Fabian1234567/Handroboter/Kostentabelle_FabianExel.pdf

Tabelle1

Kostentabelle SIA Fabian Exel
Projekt: Roboterarm Handschuh
Teil | Menge | Preis einzelnd | Preis zusammen
Servo | 3 | 15,00 € | 45,00 €
Holzplatte | 1 | 2,00 € | 2,00 €
Ständer | 1 | 1,00 € | 1,00 €
Arduino Mega | 1 | 60,00 € | 60,00 €
Handschuh | 1 | 5,00 € | 5,00 €
Kabel | | 3,00 € | 3,00 €
diverses anderes Holz | | 5,00 € | 5,00 €
Metallplatten | | 7,00 € | 7,00 €
Metallstangen | | 3,00 € | 3,00 €
Potentiometer | 2 | 0,50 € | 1,00 €
Neigunngssensor | 1 | 0,50 € | 0,50 €
diverse Schrauben | | 1,00 € | 1,00 €
Zahnräder | 3 | 0,20 € | 0,60 €
Summe: | 134,10 €

* Alle Angaben sind Schätzwerte, da die Sachen überwiegend schon vorhanden sind
