Fabian1234567/Handroboter/Abschlusspräsentation.pdf

# Was wäre, wenn Sie hier sitzen bleiben könnten, während Sie in einem anderen Klassenzimmer auf die Tafel schreiben?

# Die Lösung:

Der Robotergreifer,

# der sich wie eine Hand bewegt

# Ein SIA Projekt von Fabian Exel am Gustav Stresemann Gymnasium Fellbach-Schmiden

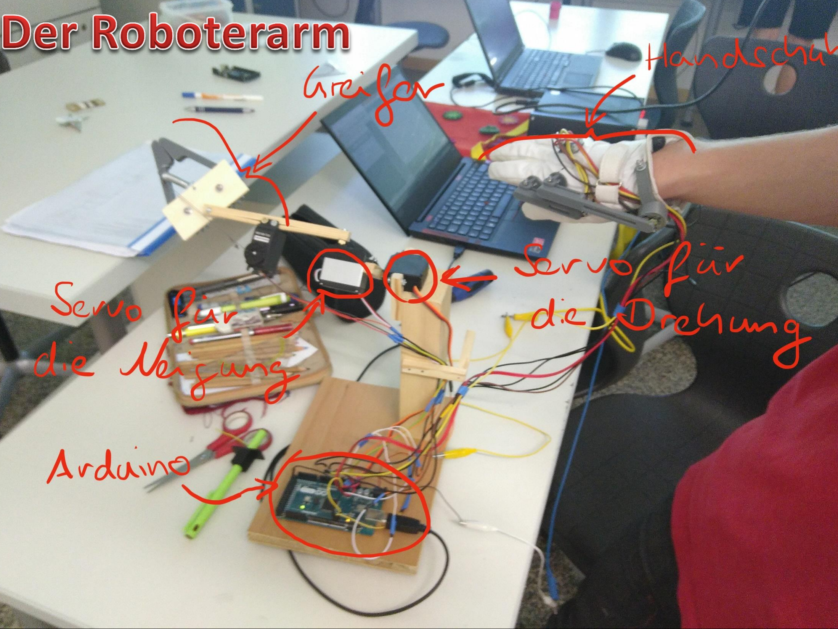
[picture p3: page 3]

# Handschuh

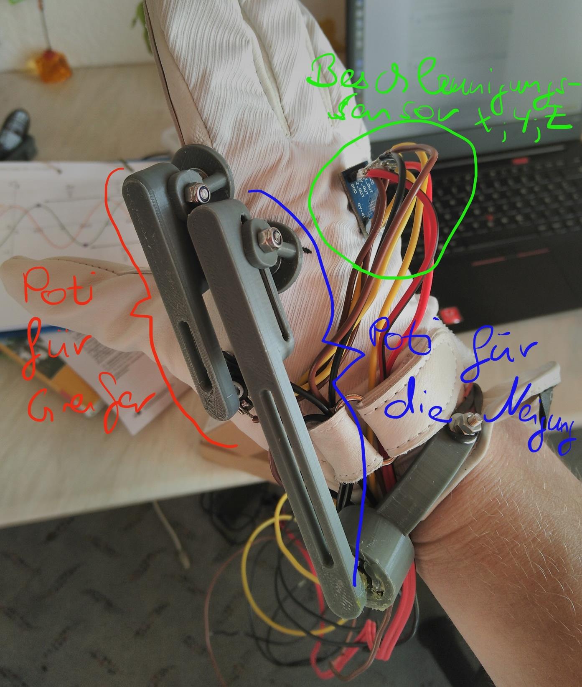
[picture p4: page 4]

# Schaltplan

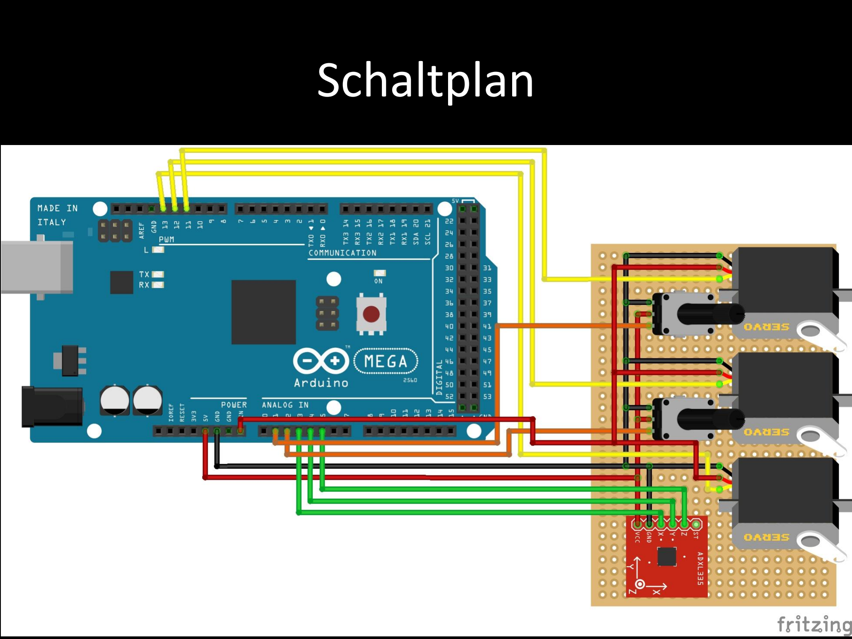
[picture p5: page 5]

# EDV

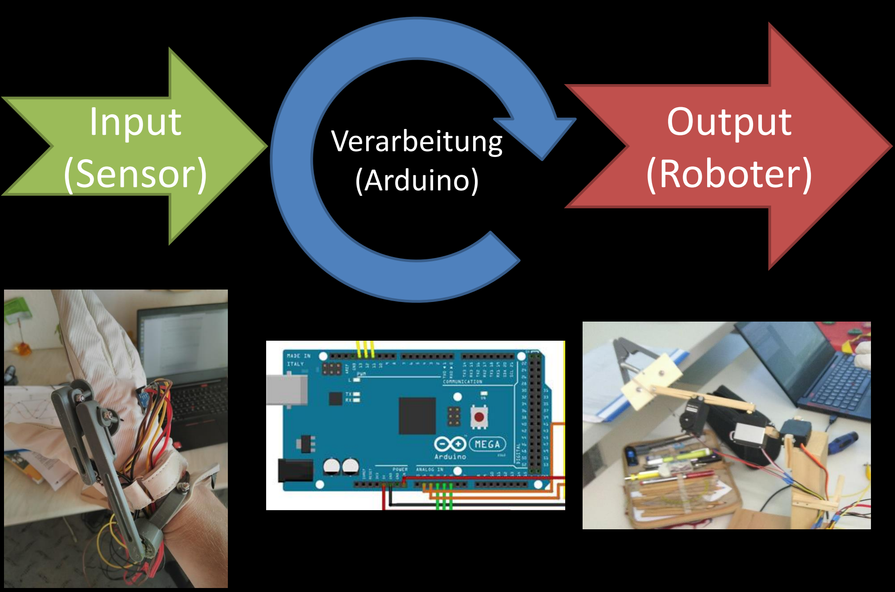
[picture p6: figure]
Input (Sensor); Verarbeitung (Arduino); Output (Roboter)

# Greifer

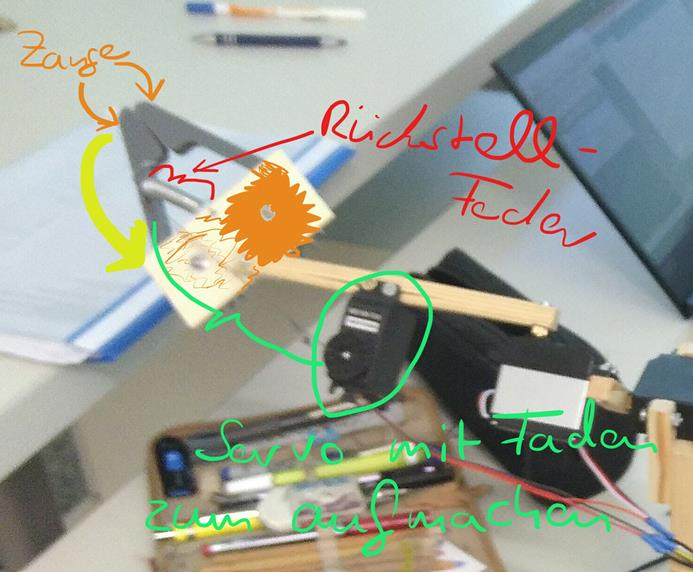
[picture p7: page 7]

# Warum Servo?

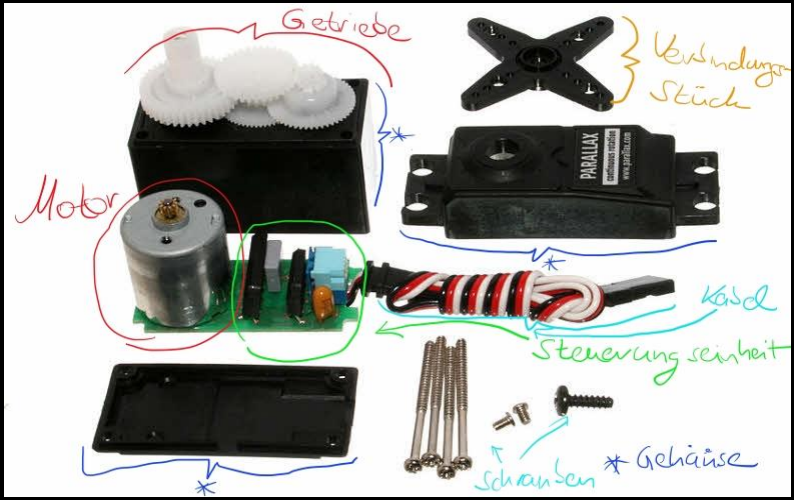
[picture p8: figure]

(https://www.precifast.de/servomotor-funktion-ansteuern-anschliessen/)

# Regelkreis des Servos

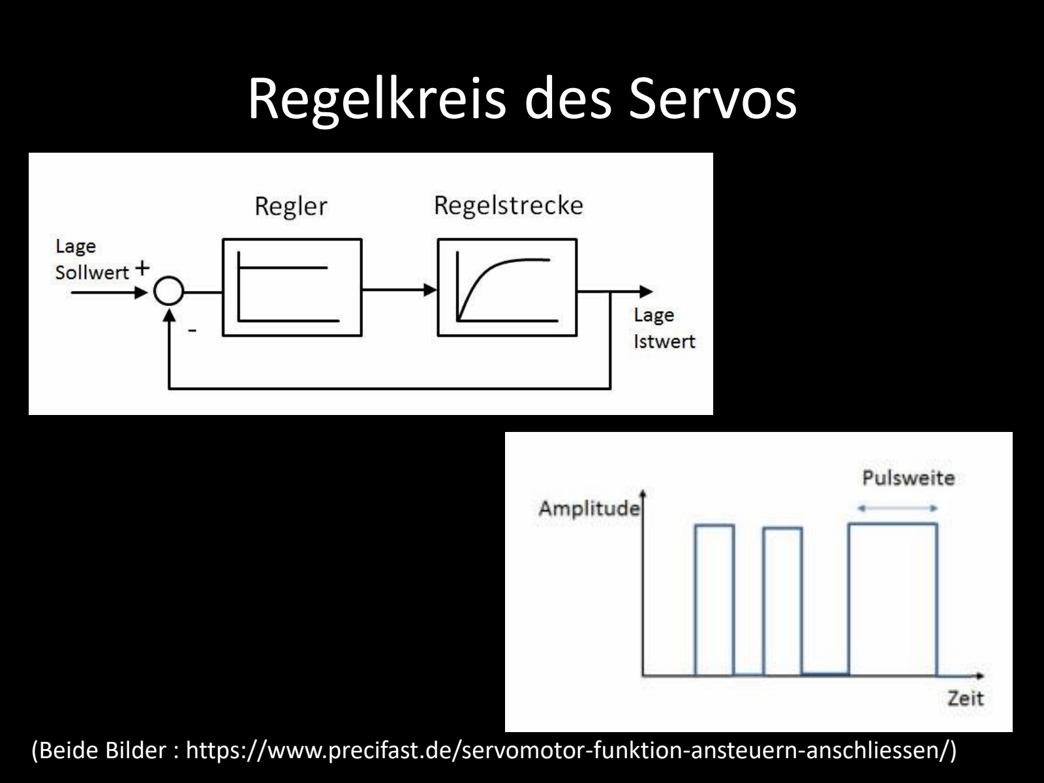
[picture p9: page 9]

(Beide Bilder : https://www.precifast.de/servomotor-funktion-ansteuern-anschliessen/)

# Warum Beschleunigungssensor?

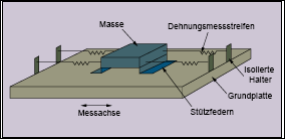
[picture p10: figure]

(https://www.omega.de/prodinfo/beschleunigungsmesser-vibrationsaufnehmer.html)

# Programmcode

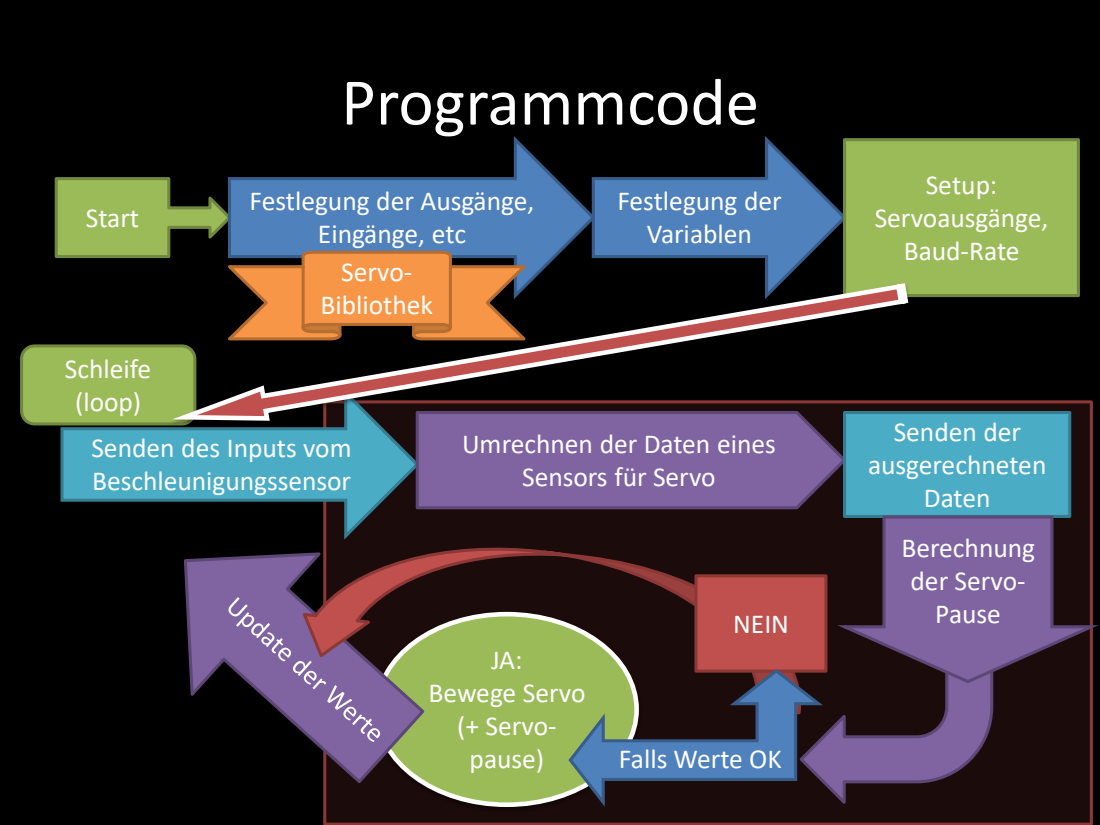
[picture p11: page 11]
Start; Festlegung der Ausgänge,; Eingänge, etc; Festlegung der Variablen; Servo- Bibliothek; Setup: Servoausgänge, Baud-Rate; Senden der ausgerechneten Daten; JA: Bewege Servo (+ Servo- pause); NEIN; Berechnung der Servo- Pause

Schleife
(loop)
Senden des Inputs vom
Beschleunigungssensor

Umrechnen der Daten eines
Sensors für Servo

Falls Werte OK

# Der wichtigste Baustein des Programms

- neigung = map(analogRead(accYPin), 270, 410, 30, 330);
- Serial.print(" Servo Neigung: ");
- Serial.print(neigung);

## - pause_neigung = abs(neigung - neigung_alt)

* 5;

## - if (pause_neigung <= 80 && neigung > 0){

- third.write(neigung);
- delay(pause_neigung);
- }
- neigung_alt = neigung;
- }

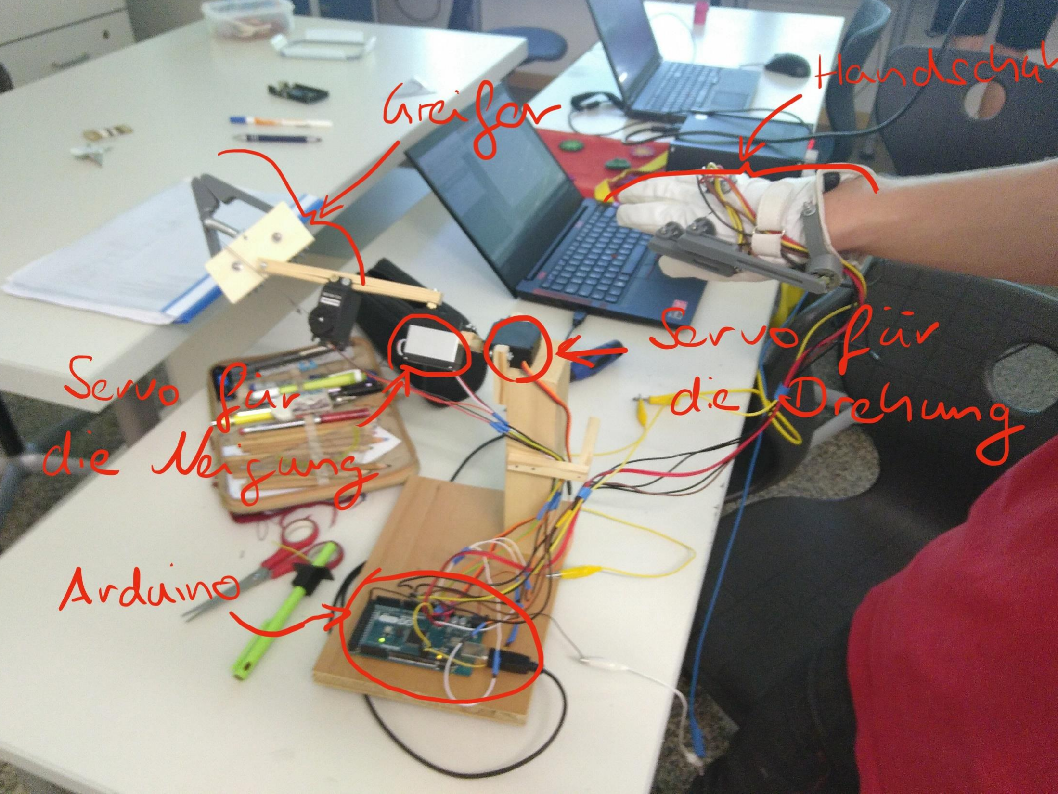
[picture p12: page 13]
